lucysrausch/pcbtc/software/Inc/device_conf.h

/*
 * device_conf.h
 *
 *  Created on: 2018/07/03
 *      Author: Keshikan
 */

#ifndef DEVICE_CONF_H_
#define DEVICE_CONF_H_

#define LED_POW_GPIO GPIOA
#define LED_POW_PIN GPIO_PIN_15

#define LED_FAULT_GPIO GPIOA
#define LED_FAULT_PIN GPIO_PIN_10

#define BUTTON_GPIO GPIOA
#define BUTTON_PIN GPIO_PIN_7

#endif /* DEVICE_CONF_H_ */
